mecparts/PicoWiFiModem/src/support.h

void doAtCmds(char *atCmd);             // forward delcaration

void crlf(void) {
   uart_puts(uart0, "\r\n");
}

uint32_t getTotalHeap(void) {
   extern char __StackLimit, __bss_end__;
   
   return &__StackLimit  - &__bss_end__;
}

uint32_t getFreeHeap(void) {
   struct mallinfo m = mallinfo();

   return getTotalHeap() - m.uordblks;
}

uint32_t getProgramSize(void) {
   extern char __flash_binary_start, __flash_binary_end;

   return &__flash_binary_end - &__flash_binary_start;
}

uint32_t getFreeProgramSpace() {
   return PICO_FLASH_SIZE_BYTES - getProgramSize();
}

// DTR low to high interrupt handler
void dtrIrq(uint gpio, uint32_t events) {
   if( gpio == DTR && (events & GPIO_IRQ_EDGE_RISE) ) {
      dtrWentInactive = true;
   }
}

// return and reset DTR change indicator
bool checkDtrIrq(void) {
   bool ret = dtrWentInactive;
   dtrWentInactive = false;
   return ret;
}

//
// We're in local command mode. Assemble characters from the
// serial port into a buffer for processing.
//
void inAtCommandMode() {
   char c;

   // get AT command
   if( uart_is_readable(uart0) ) {
      c = uart_getc(uart0);

      if( c == LF || c == CR ) {       // command finished?
         if( settings.echo ) {
            crlf();
         }
         doAtCmds(atCmd);               // yes, then process it
         atCmd[0] = NUL;
         atCmdLen = 0;
      } else if( (c == BS || c == DEL) && atCmdLen > 0 ) {
         atCmd[--atCmdLen] = NUL;      // remove last character
         if( settings.echo ) {
            printf("\b \b");
         }
      } else if( c == '/' && atCmdLen == 1 && toupper(atCmd[0]) == 'A' && lastCmd[0] != NUL ) {
         if( settings.echo ) {
            printf("/\r\n");
         }
         strncpy(atCmd, lastCmd, sizeof atCmd);
         atCmd[MAX_CMD_LEN] = NUL;
         doAtCmds(atCmd);                  // repeat last command
         atCmd[0] = NUL;
         atCmdLen = 0;
      } else if( c >=' ' && c <= '~' ) {  // printable char?
         if( atCmdLen < MAX_CMD_LEN ) {
            atCmd[atCmdLen++] = c;        // add to command string
            atCmd[atCmdLen] = NUL;
         }
         if( settings.echo ) {
            uart_putc(uart0, c);
         }
      }
   }
}

//
// send serial data to the TCP client
//
void sendSerialData() {
   static uint32_t lastSerialData = 0;
   // in telnet mode, we might have to escape every single char,
   // so don't use more than half the buffer
   size_t maxBufSize = (sessionTelnetType != NO_TELNET) ? TX_BUF_SIZE / 2 : TX_BUF_SIZE;
   size_t len = uart_is_readable(uart0);
   if( len > maxBufSize) {
      len = maxBufSize;
   }
   uint8_t *p = txBuf;
   for( size_t i = 0; i < len; ++i ) {
      *p++ = uart_getc(uart0);
   }

   uint32_t serialInterval = millis() - lastSerialData;
   // if more than 1 second since the last character,
   // start the online escape sequence counter over again
   if( escCount && serialInterval >= GUARD_TIME ) {
      escCount = 0;
   }
   if( settings.escChar < 128 && (escCount || serialInterval >= GUARD_TIME) ) {
      // check for the online escape sequence
      // +++ with a 1 second pause before and after
      // if escape character is >= 128, it's ignored
      for( size_t i = 0; i < len; ++i ) {
         if( txBuf[i] == settings.escChar ) {
            if( ++escCount == ESC_COUNT ) {
               guardTime = millis() + GUARD_TIME;
            } else {
               guardTime = 0;
            }
         } else {
            escCount = 0;
         }
      }
   } else {
      escCount = 0;
   }
   lastSerialData = millis();

   // in Telnet mode, escape every IAC (0xff) by inserting another
   // IAC after it into the buffer (this is why we only read up to
   // half of the buffer in Telnet mode)
   //
   // also in Telnet mode, escape every CR (0x0D) by inserting a NUL
   // after it into the buffer
   if( sessionTelnetType != NO_TELNET ) {
      for( int i = len - 1; i >= 0; --i ) {
         if( txBuf[i] == IAC ) {
            memmove( txBuf + i + 1, txBuf + i, len - i);
            ++len;
         } else if( txBuf[i] == CR && sessionTelnetType == REAL_TELNET ) {
            memmove( txBuf + i + 1, txBuf + i, len - i);
            txBuf[i + 1] = NUL;
            ++len;
         }
      }
   }
   bytesOut += tcpWriteBuf(tcpClient, txBuf, len);
}

//
// Receive data from the TCP client
//
// We do some limited processing of in band Telnet commands.
// Specifically, we handle the following commanads: BINARY,
// ECHO, SUP_GA (suppress go ahead), TTYPE (terminal type),
// TSPEED (terminal speed), LOC (terminal location) and
// NAWS (terminal columns and rows).
//
int receiveTcpData() {
   static char lastc = 0;
   uint8_t txBuf[256];
   uint16_t txLen;
   
   int rxByte = tcpReadByte(tcpClient);
   ++bytesIn;

   if( sessionTelnetType != NO_TELNET && rxByte == IAC ) {
      rxByte = tcpReadByte(tcpClient, 1000);
      ++bytesIn;
      if( rxByte == DM ) { // ignore data marks
         rxByte = -1;
      } else if( rxByte == BRK ) { // break?
         uart_set_break(uart0, true);
         sleep_ms(300);
         uart_set_break(uart0, false);
         rxByte = -1;
      } else if( rxByte == AYT ) { // are you there?
#ifndef NDEBUG
         char tBuf[160];
         snprintf(tBuf,sizeof tBuf, "\r\nrxLen: %u rxHead: %u rxTail: %u\r\ntxLen: %u, txHead: %u, txTail:%u\r\n",
            tcpClient->rxBuffLen, tcpClient->rxBuffHead, tcpClient->rxBuffTail,
            tcpClient->txBuffLen, tcpClient->txBuffHead, tcpClient->txBuffTail);
         bytesOut += tcpWriteStr(tcpClient, tBuf);
         snprintf(tBuf,sizeof tBuf, "maxTotLen: %u\r\nmaxRxBuffLen: %u\r\nmaxTxBuffLen: %u\r\n",
            maxTotLen, maxRxBuffLen, maxTxBuffLen);
         bytesOut += tcpWriteStr(tcpClient, tBuf);
         if( lastTcpWriteErr != ERR_OK ) {
            snprintf(tBuf, sizeof tBuf, "lastTcpWriteErr: %d\r\n", lastTcpWriteErr);
            lastTcpWriteErr = ERR_OK;
            bytesOut += tcpWriteStr(tcpClient, tBuf);
         }
         if( gpio_get_out_level(RXBUFF_OVFL) ) {
            gpio_put(RXBUFF_OVFL, LOW);
            bytesOut += tcpWriteStr(tcpClient,"RXBUFF_OVFL\r\n");
         }
         if( gpio_get_out_level(TXBUFF_OVFL) ) {
            gpio_put(TXBUFF_OVFL, LOW);
            bytesOut += tcpWriteStr(tcpClient,"TXBUFF_OVFL\r\n");
         }
#else
         bytesOut += tcpWriteStr(tcpClient, "\r\n[Yes]\r\n");
#endif
         rxByte = -1;
      } else if( rxByte != IAC ) { // 2 times 0xff is just an escaped real 0xff
         // rxByte has now the first byte of the actual non-escaped control code
#if IAC_DEBUG
         printf("[%u,", rxByte);
#endif
         uint8_t cmdByte1 = rxByte;
         if( cmdByte1 == DO || cmdByte1 == DONT || cmdByte1 == WILL || cmdByte1 == WONT || cmdByte1 == SB ) {
            rxByte = tcpReadByte(tcpClient, 1000);
            ++bytesIn;
         }
         uint8_t cmdByte2 = rxByte;
#if IAC_DEBUG
         printf("%u",rxByte);
#endif
         txLen = 0;
         switch( cmdByte1 ) {
            case DO:
               switch( cmdByte2 ) {
                  case BINARY:
                  case ECHO:
                  case SUP_GA:
                  case TTYPE:
                  case TSPEED:
                     if( amClient || (cmdByte2 != SUP_GA && cmdByte2 != ECHO) ) {
                        // in a server connection, we've already sent out
                        // WILL SUP_GA and WILL ECHO so we shouldn't again
                        // to prevent an endless round robin of WILLs and
                        // DOs SUP_GA/ECHO echoing back and forth
                        txBuf[txLen++] = IAC;
                        txBuf[txLen++] = WILL;
                        txBuf[txLen++] = cmdByte2;
                        bytesOut += tcpWriteBuf(tcpClient, txBuf, txLen);
                     }
                     break;
                  case LOC:
                  case NAWS:
                     txBuf[txLen++] = IAC;
                     txBuf[txLen++] = WILL;
                     txBuf[txLen++] = cmdByte2;
                     txBuf[txLen++] = IAC;
                     txBuf[txLen++] = SB;
                     txBuf[txLen++] = cmdByte2;

                     switch( cmdByte2 ) {
                        case NAWS:     // window size
                           txBuf[txLen++] = (uint8_t)0;
                           txBuf[txLen++] = settings.width;
                           txBuf[txLen++] = (uint8_t)0;
                           txBuf[txLen++] = settings.height;
                           break;
                        case LOC:      // terminal location
                           txLen += snprintf((char *)txBuf+txLen, (sizeof txBuf)-txLen, "%s", settings.location);
                           break;
                     }
                     txBuf[txLen++] = IAC;
                     txBuf[txLen++] = SE;
                     bytesOut += tcpWriteBuf(tcpClient, txBuf, txLen);
                     break;
                  default:
                     txBuf[txLen++] = IAC;
                     txBuf[txLen++] = WONT;
                     txBuf[txLen++] = cmdByte2;
                     bytesOut += tcpWriteBuf(tcpClient, txBuf, txLen);
                     break;
               }
               break;
            case WILL:
               // Server wants to do option, allow most
               txBuf[txLen++] = IAC;
               switch( cmdByte2 ) {
                  case LINEMODE:
                  case NAWS:
                  case LFLOW:
                  case NEW_ENVIRON:
                  case XDISPLOC:
                     txBuf[txLen++] = DONT;
                     break;
                  default:
                     txBuf[txLen++] = DO;
                     break;
               }
               txBuf[txLen++] = cmdByte2;
               bytesOut += tcpWriteBuf(tcpClient, txBuf, txLen);
               break;
            case SB:
               switch( cmdByte2 ) {
                  case TTYPE:
                  case TSPEED:
                     do {
                        rxByte = tcpReadByte(tcpClient, 10);
                        if( rxByte != -1 ) {
                           ++bytesIn;
                        }
                     } while( rxByte != SE ); // discard rest of cmd
                     txBuf[txLen++] = IAC;
                     txBuf[txLen++] = SB;
                     txBuf[txLen++] = cmdByte2;
                     txBuf[txLen++] = VLSUP;
                     switch( cmdByte2 ) {
                        case TTYPE:    // terminal type
                           txLen += snprintf( (char *)txBuf+txLen, (sizeof txBuf)-txLen, "%s", settings.terminal);
                           break;
                        case TSPEED:   // terminal speed
                           txLen += snprintf( (char *)txBuf+txLen, (sizeof txBuf)-txLen, "%lu,%lu", settings.serialSpeed, settings.serialSpeed);
                           break;
                     }
                     txBuf[txLen++] = IAC;
                     txBuf[txLen++] = SE;
                     bytesOut += tcpWriteBuf(tcpClient, txBuf, txLen);
                     break;
                  default:
                     break;
               }
               break;
         }
         rxByte = -1;
      }
#if IAC_DEBUG
      printf("]");
#endif
   }
   // Telnet sends <CR> as <CR><NUL>
   // We filter out that <NUL> here
   if( lastc == CR && (char)rxByte == 0 && sessionTelnetType == REAL_TELNET ) {
      rxByte = -1;
   }
   lastc = (char)rxByte;
   return rxByte;
}

//
// return a pointer to a string containing the connect time of the last session
//
char *connectTimeString(void) {
   unsigned long now = millis();
   int hours, mins, secs;
   static char result[9];

   if( connectTime ) {
      secs = (now - connectTime) / 1000;
      mins = secs / 60;
      hours = mins / 60;
      secs %= 60;
      mins %= 60;
   } else {
      hours = mins = secs = 0;
   }
   result[0] = (char)(hours / 10 + '0');
   result[1] = (char)(hours % 10 + '0');
   result[2] = ':';
   result[3] = (char)(mins / 10 + '0');
   result[4] = (char)(mins % 10 + '0');
   result[5] = ':';
   result[6] = (char)(secs / 10 + '0');
   result[7] = (char)(secs % 10 + '0');
   result[8] = NUL;
   return result;
}

//
// print a result code/string to the serial port
//
void sendResult(int resultCode) {
   if( !settings.quiet ) {             // quiet mode on?
      crlf();                   // no, we're going to display something
      if( !settings.verbose ) {
         if( resultCode == R_RING_IP ) {
            resultCode = R_RING;
         }
         printf("%d\r\n", resultCode);   // not verbose, just print the code #
      } else {
         switch( resultCode ) {        // possible extra info for CONNECT and
                                       // NO CARRIER if extended codes are
            case R_CONNECT:            // enabled
               uart_puts(uart0, connectStr);
               if( settings.extendedCodes ) {
                  printf(" %lu", settings.serialSpeed);
               }
               break;

            case R_NO_CARRIER:
               uart_puts(uart0, noCarrierStr);
               if( settings.extendedCodes ) {
                  printf(" (%s)", connectTimeString());
               }
               break;

            case R_ERROR:
               uart_puts(uart0, errorStr);
               lastCmd[0] = NUL;
               memset(atCmd, 0, sizeof atCmd);
               break;

            case R_RING_IP:
               uart_puts(uart0, ringStr);
               if( settings.extendedCodes ) {
                  printf(" %s", ip4addr_ntoa(&tcpClient->pcb->remote_ip));
               }
               break;

            default:
               uart_puts(uart0, resultCodes[resultCode]);
               break;
         }
         crlf();
      }
   } else if( resultCode == R_ERROR ) {
      lastCmd[0] = NUL;
      memset(atCmd, 0, sizeof atCmd);
   }
   if( resultCode == R_NO_CARRIER || resultCode == R_NO_ANSWER ) {
      sessionTelnetType = settings.telnet;
   }
}

//
// terminate an active call
//
void endCall() {
   state = CMD_NOT_IN_CALL;
   tcpClientClose(tcpClient);
   tcpClient = NULL;
   sendResult(R_NO_CARRIER);
   gpio_put(DCD, !ACTIVE);
   connectTime = 0;
   escCount = 0;
}

//
// Check for an incoming TCP session. There are 3 scenarios:
//
// 1. We're already in a call, or auto answer is disabled and the
//    ring count exceeds the limit: tell the caller we're busy.
// 2. We're not in a call and auto answer is disabled, or the #
//    of rings is less than the auto answer count: either start
//    or continue ringing.
// 3. We're no in a call, auto answer is enabled and the # of rings
//    is at least the auto answer count: answer the call.
//
void checkForIncomingCall() {
   if( settings.listenPort && serverHasClient(&tcpServer) ) {
      if( state != CMD_NOT_IN_CALL || (!settings.autoAnswer && ringCount > MAGIC_ANSWER_RINGS) ) {
         gpio_put(RI, !ACTIVE);
         TCP_CLIENT_T *droppedClient = serverGetClient(&tcpServer, &tcpDroppedClient);
         if( settings.busyMsg[0] ) {
            tcpWriteStr(droppedClient, settings.busyMsg);
            tcpWriteStr(droppedClient, "\r\nCurrent call length: ");
            tcpWriteStr(droppedClient, connectTimeString());
         } else {
            tcpWriteStr(droppedClient, "BUSY");
         }
         tcpWriteStr(droppedClient, "\r\n\r\n");
         tcpTxFlush(droppedClient);
         tcpClientClose(droppedClient);
         ringCount = 0;
         ringing = false;
      } else if( !settings.autoAnswer || ringCount < settings.autoAnswer ) {
         if( !ringing ) {
            ringing = true;            // start ringing
            ringCount = 1;
            gpio_put(RI, ACTIVE);
            if( !settings.autoAnswer || ringCount < settings.autoAnswer ) {
               sendResult(R_RING);     // only show RING if we're not just
            }                          // about to answer
            nextRingMs = millis() + RING_INTERVAL;
         } else if( millis() > nextRingMs ) {
            if( gpio_get(RI) == ACTIVE ) {
               gpio_put(RI, !ACTIVE);
            } else {
               ++ringCount;
               gpio_put(RI, ACTIVE);
               if( !settings.autoAnswer || ringCount < settings.autoAnswer ) {
                  sendResult(R_RING);
               }
            }
            nextRingMs = millis() + RING_INTERVAL;
         }
      } else if( settings.autoAnswer && ringCount >= settings.autoAnswer ) {
         gpio_put(RI, !ACTIVE);
         tcpClient = serverGetClient(&tcpServer, &tcpClient0);
         if( settings.telnet != NO_TELNET ) {
            // send incantation to switch from line mode to character mode
            bytesOut += tcpWriteBuf(tcpClient, toCharModeMagic, sizeof toCharModeMagic);
         }
         sendResult(R_RING_IP);
         gpio_put(DCD, ACTIVE);
         if( settings.serverPassword[0]) {
            tcpWriteStr(tcpClient, "\r\r\nPassword: ");
            state = PASSWORD;
            passwordTries = 0;
            passwordLen = 0;
            password[0] = NUL;
         } else {
            sleep_ms(1000);
            state = ONLINE;
            amClient = false;
            dtrWentInactive = false;
            sendResult(R_CONNECT);
         }
         connectTime = millis();
      }
   } else if( ringing ) {
      gpio_put(RI, !ACTIVE);
      ringing = false;
      ringCount = 0;
   }
}

#if OTA_UPDATE_ENABLED
//
// setup for OTA sketch updates
//
void setupOTAupdates() {
   ArduinoOTA.setHostname(settings.mdnsName);

   ArduinoOTA.onStart([]() {
      printf("OTA upload start\r\n");
      gpio_put(DSR, !ACTIVE);
   });

   ArduinoOTA.onEnd([]() {
      printf("OTA upload end - programming\r\n"));
      uart_tx_wait_blocking(uart0); // allow serial output to finish
      gpio_put(TXEN, HIGH);         // before disabling the TX output
   });

   ArduinoOTA.onProgress([](unsigned int progress, unsigned int total) {
      unsigned int pct = progress / (total / 100);
      static unsigned int lastPct = 999;
      if( pct != lastPct ) {
         lastPct = pct;
         if( settings.serialSpeed >= 4800 || pct % 10 == 0 ) {
            printf("Progress: %u%%\r", pct);
         }
      }
   });

   ArduinoOTA.onError([](ota_error_t errorno) {
      print("OTA Error - ");
      switch( errorno ) {
         case OTA_AUTH_ERROR:
            printf("Auth failed\r\n");
            break;
         case OTA_BEGIN_ERROR:
            printf("Begin failed\r\n");
            break;
         case OTA_CONNECT_ERROR:
            printf("Connect failed\r\n");
            break;
         case OTA_RECEIVE_ERROR:
            printf("Receive failed\r\n");
            break;
         case OTA_END_ERROR:
            printf("End failed\r\n");
            break;
         default:
            printf("Unknown (%u)\r\n", errorno);
            break;
      }
      sendResult(R_ERROR);
   });
   ArduinoOTA.begin();
}
#endif

void setHardwareFlow(bool state) {
   if( state ) {
      gpio_set_function(CTS, GPIO_FUNC_UART);
      gpio_set_function(RTS, GPIO_FUNC_UART);
   } else {
      gpio_init(CTS);
      gpio_init(RTS);
      gpio_set_dir(CTS, OUTPUT);
      gpio_put(CTS, ACTIVE);
      gpio_set_dir(RTS, INPUT);
   }
   uart_set_hw_flow(uart0, state, state);


}

// trim leading and trailing blanks from a string
void trim(char *str) {
   char *trimmed = str;
   // find first non blank character
   while( *trimmed && isspace(*trimmed) ) {
      ++trimmed;
   }
   if( *trimmed ) {
      // trim off any trailing blanks
      for( int i = strlen(trimmed) - 1; i >= 0; --i ) {
         if( isspace(trimmed[i]) ) {
            trimmed[i] = NUL;
         } else {
            break;
         }
      }
   }
   // shift string only if we had leading blanks
   if( str != trimmed ) {
      int i, len = strlen(trimmed);
      for( i = 0; i < len; ++i ) {
         str[i] = trimmed[i];
      }
      str[i] = NUL;
   }
}

//
// Parse a string in the form "hostname[:port]" and return
//
// 1. A pointer to the hostname
// 2. A pointer to the optional port
// 3. The numeric value of the port (if not specified, 23)
//
void getHostAndPort(char *number, char* &host, char* &port, int &portNum) {
   char *ptr;

   port = strrchr(number, ':');
   if( !port ) {
      portNum = TELNET_PORT;
   } else {
      *port++ = NUL;
      portNum = atoi(port);
   }
   host = number;
   while( *host && isspace(*host) ) {
      ++host;
   }
   ptr = host;
   while( *ptr && !isspace(*ptr) ) {
      ++ptr;
   }
   *ptr = NUL;
}

//
// Display the operational settings
//
void displayCurrentSettings(void) {
   printf("Active Profile:\r\n");
   printf("Baud.......: %lu\r\n", settings.serialSpeed);
   printf("SSID.......: %s\r\n", settings.ssid);
   printf("Pass.......: %s\r\n", settings.wifiPassword);
   printf("mDNS name..: %s.local\r\n", settings.mdnsName);
   printf("Server port: %u\r\n", settings.listenPort);
   printf("Busy msg...: %s\r\n", settings.busyMsg);
   printf("E%u Q%u V%u X%u &D%u &K%u NET%u S0=%u S2=%u\r\n",
      settings.echo,
      settings.quiet,
      settings.verbose,
      settings.extendedCodes,
      settings.dtrHandling,
      settings.rtsCts,
      settings.telnet,
      settings.autoAnswer,
      settings.escChar);

   printf("Speed dial:\r\n");
   for( int i = 0; i < SPEED_DIAL_SLOTS; ++i ) {
      if( settings.speedDial[i][0] ) {
         printf("%u: %s,%s\r\n",
            i, settings.speedDial[i], settings.alias[i]);
      }
   }
}

//
// Display the settings stored in flash (NVRAM).
//
void displayStoredSettings(void) {
   SETTINGS_T temp;

   readSettings(&temp);
   printf("Stored Profile:\r\n");
   printf("Baud.......: %lu\r\n", temp.serialSpeed);
   printf("SSID.......: %s\r\n", temp.ssid);
   printf("Pass.......: %s\r\n", temp.wifiPassword);
   printf("mDNS name..: %s.local\r\n", temp.mdnsName);
   printf("Server port: %u\r\n", temp.listenPort);
   printf("Busy Msg...: %s\r\n", temp.busyMsg);
   printf("E%u Q%u V%u X%u &D%u &K%u NET%u S0=%u S2=%u\r\n",
      temp.echo, 
      temp.quiet,
      temp.verbose,
      temp.extendedCodes,
      temp.dtrHandling,
      temp.rtsCts,
      temp.telnet,
      temp.autoAnswer,
      temp.escChar);

   printf("Speed dial:\r\n");
   for (int i = 0; i < SPEED_DIAL_SLOTS; i++) {
      if( temp.speedDial[i][0] ) {
         printf("%u: %s,%s\r\n", i, temp.speedDial[i], temp.alias[i]);
      }
   }
}

//
// Password is set for incoming connections.
// Allow 3 tries or 60 seconds before hanging up.
//
void inPasswordMode() {
   if( tcpBytesAvailable(tcpClient) ) {
      int c = receiveTcpData();
      switch( c ) {
         case -1:    // telnet control sequence: no data returned
            break;

         case LF:
         case CR:
            tcpWriteStr(tcpClient, "\r\n");
            if( strcmp(settings.serverPassword, password) ) {
               ++passwordTries;
               password[0] = NUL;
               passwordLen = 0;
               tcpWriteStr(tcpClient, "\r\nPassword: ");
            } else {
               state = ONLINE;
               amClient = false;;
               dtrWentInactive = false;
               sendResult(R_CONNECT);
               tcpWriteStr(tcpClient,"Welcome\r\n");
            }
            break;

         case BS:
         case DEL:
            if( passwordLen ) {
               password[--passwordLen] = NUL;
               tcpWriteStr(tcpClient, "\b \b");
            }
            break;

         default:
            if( isprint((char)c) && passwordLen < MAX_PWD_LEN ) {
               tcpWriteByte(tcpClient, '*');
               password[passwordLen++] = (char)c;
               password[passwordLen] = 0;
            }
            break;
      }
   }
   if( millis() - connectTime > PASSWORD_TIME || passwordTries >= PASSWORD_TRIES ) {
      tcpWriteStr(tcpClient, "Good-bye\r\n");
      endCall();
   } else if( !tcpIsConnected(tcpClient) ) {   // no client?
      endCall();                           // then hang up
   }
}

//
// Paged text output: using the terminal rows defined in
// settings.height, these routines pause the output when
// a screen full of text has been shown.
//
// Call with PagedOut("text", true); to initialise the
// line counter.
//
static uint8_t numLines = 0;

static bool PagedOut(const char *str, bool reset=false) {
   char c = ' ';

   if( reset ) {
      numLines = 0;
   }
   if( numLines >= settings.height-1 ) {
      printf("[More]");
      while( !uart_is_readable(uart0) );
      c = uart_getc(uart0);
      printf("\r      \r");
      numLines = 0;
   }
   if( c != CTLC ) {
      printf("%s\r\n", str);
      ++numLines;
   }
   return c == CTLC;
}
